juliendorra/3D-printable-sound-absorbers/pictures/Photo 11-07-2016 18 31 54.jpg

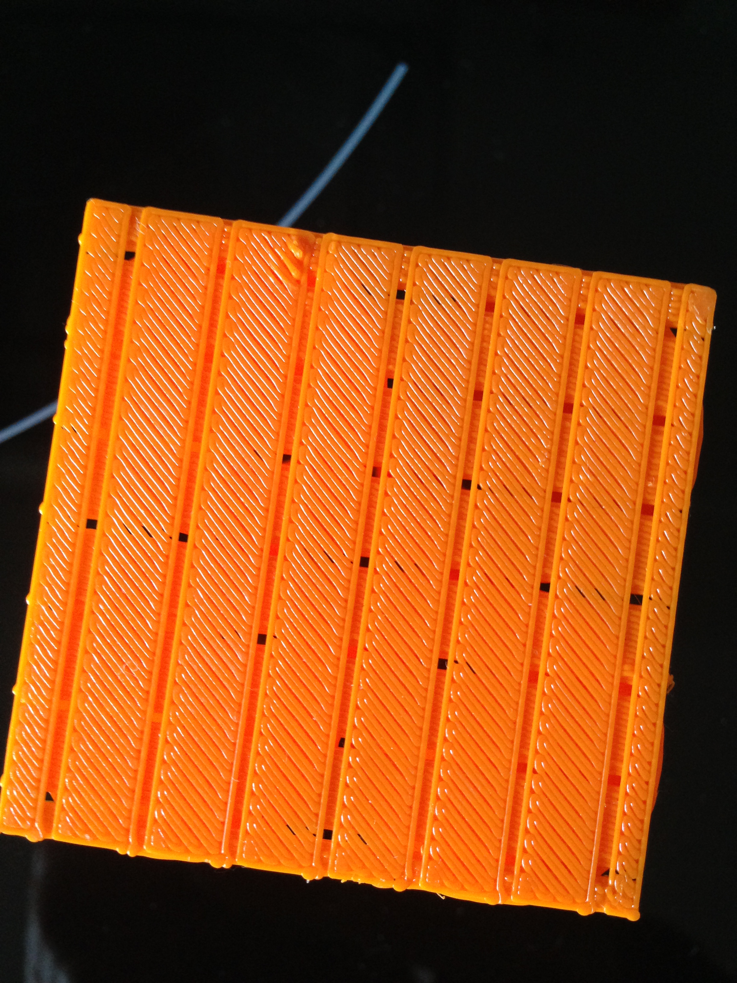
pictures/Photo 11-07-2016 18 31 54.jpg
