juliendorra/3D-printable-sound-absorbers/pictures/Photo 11-07-2016 18 33 41.jpg

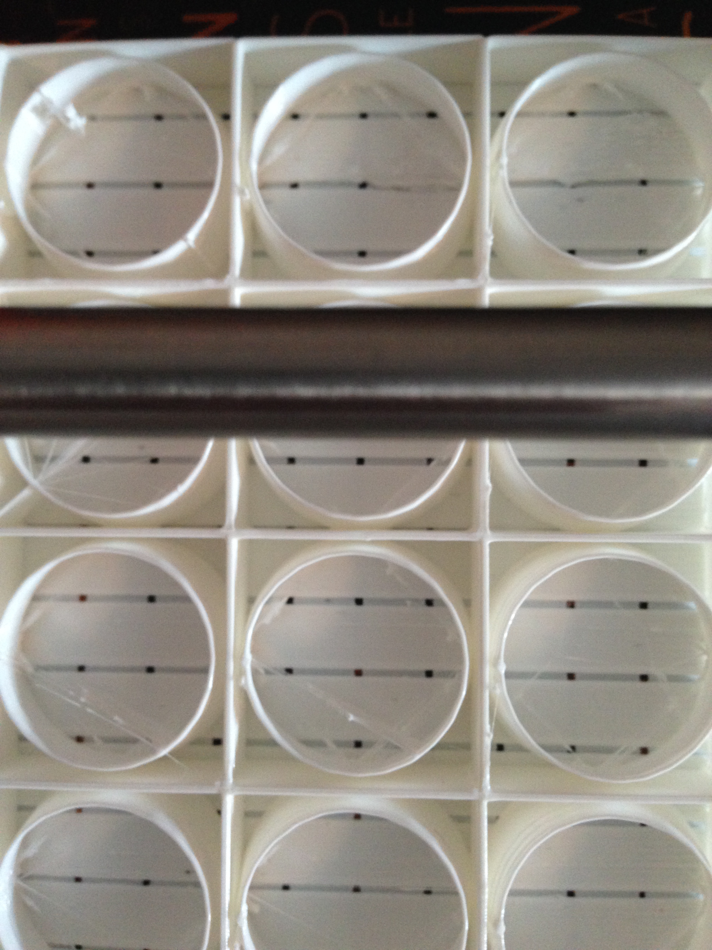
pictures/Photo 11-07-2016 18 33 41.jpg
