juliendorra/3D-printable-sound-absorbers/pictures/Photo 12-07-2016 12 48 24.jpg

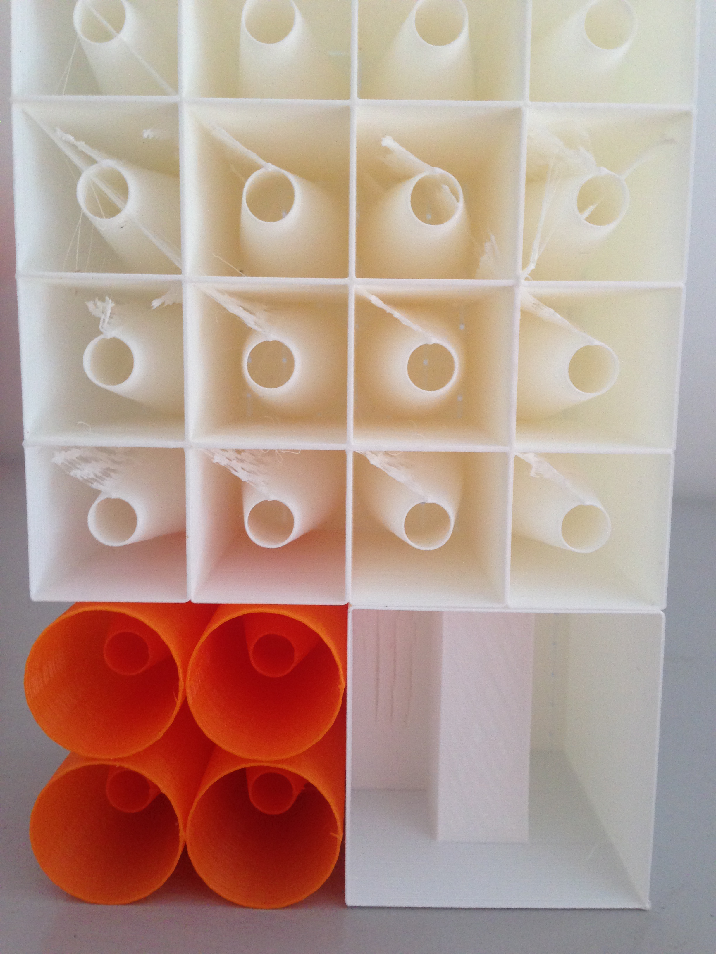
pictures/Photo 12-07-2016 12 48 24.jpg
