juliendorra/3D-printable-sound-absorbers/pictures/Photo 12-07-2016 12 48 54.jpg

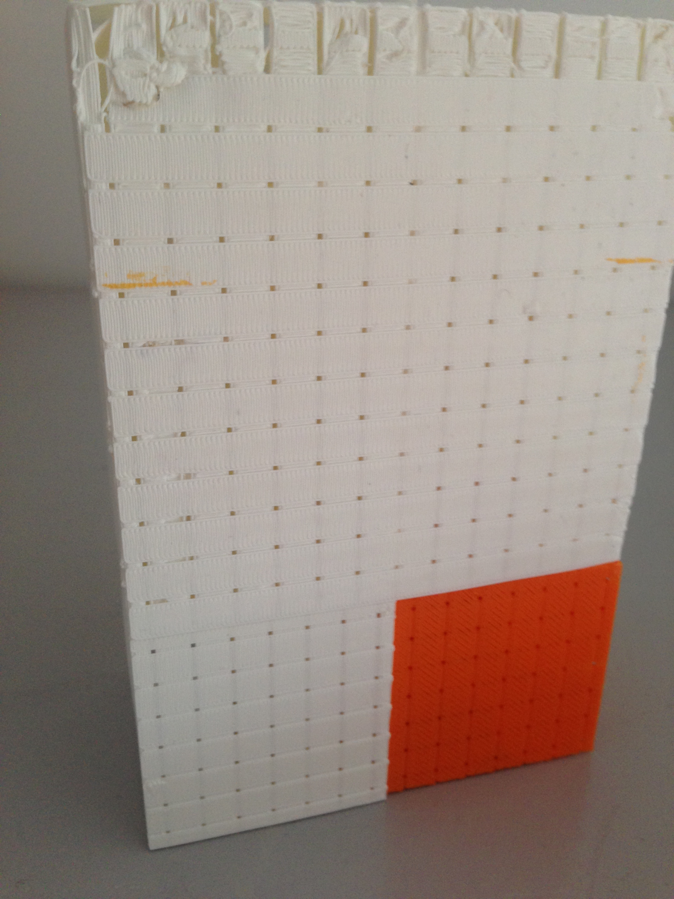
pictures/Photo 12-07-2016 12 48 54.jpg
