juliendorra/3D-printable-sound-absorbers/pictures/Photo 15-07-2016 20 15 22.jpg

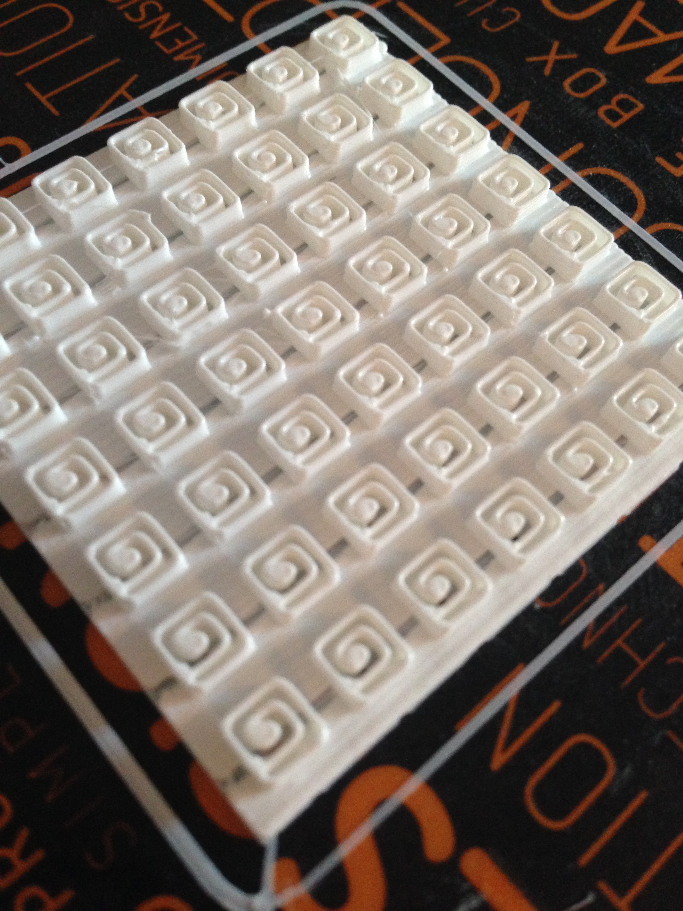
pictures/Photo 15-07-2016 20 15 22.jpg
